TwinSailsStudios/DSH-AEGIS/assets/1783966047461_image.png

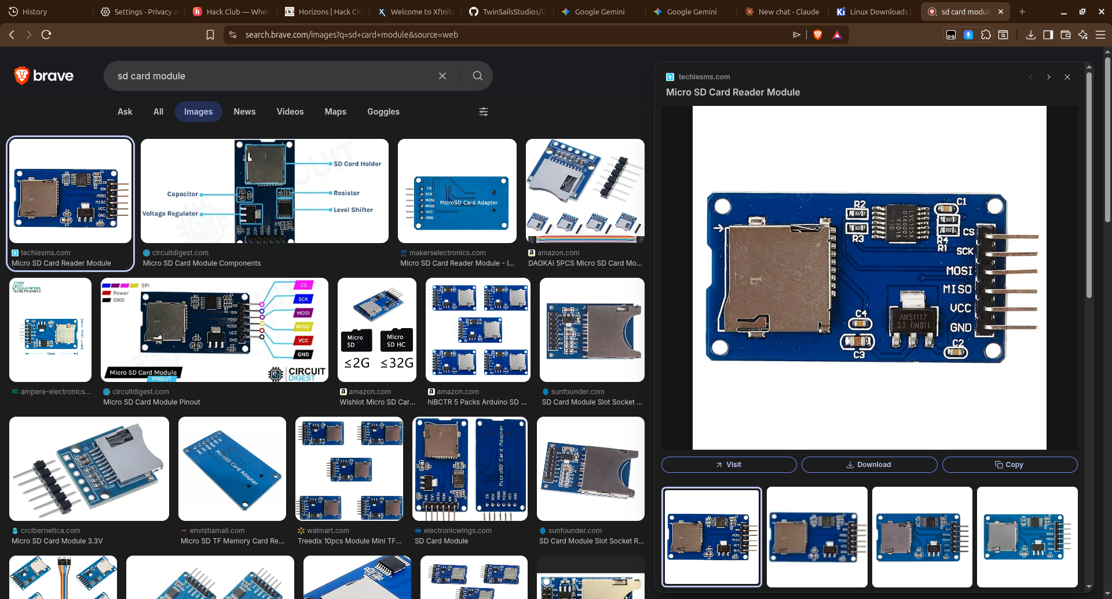
assets/1783966047461_image.png
